queueRAM/ti_graph_link/schematics/ti_graph_link_serial_black/ti_graph_link_serial_black.kicad_sch

## KiCad design schematics/ti_graph_link_serial_black/ti_graph_link_serial_black.kicad_sch (2023-08-06)

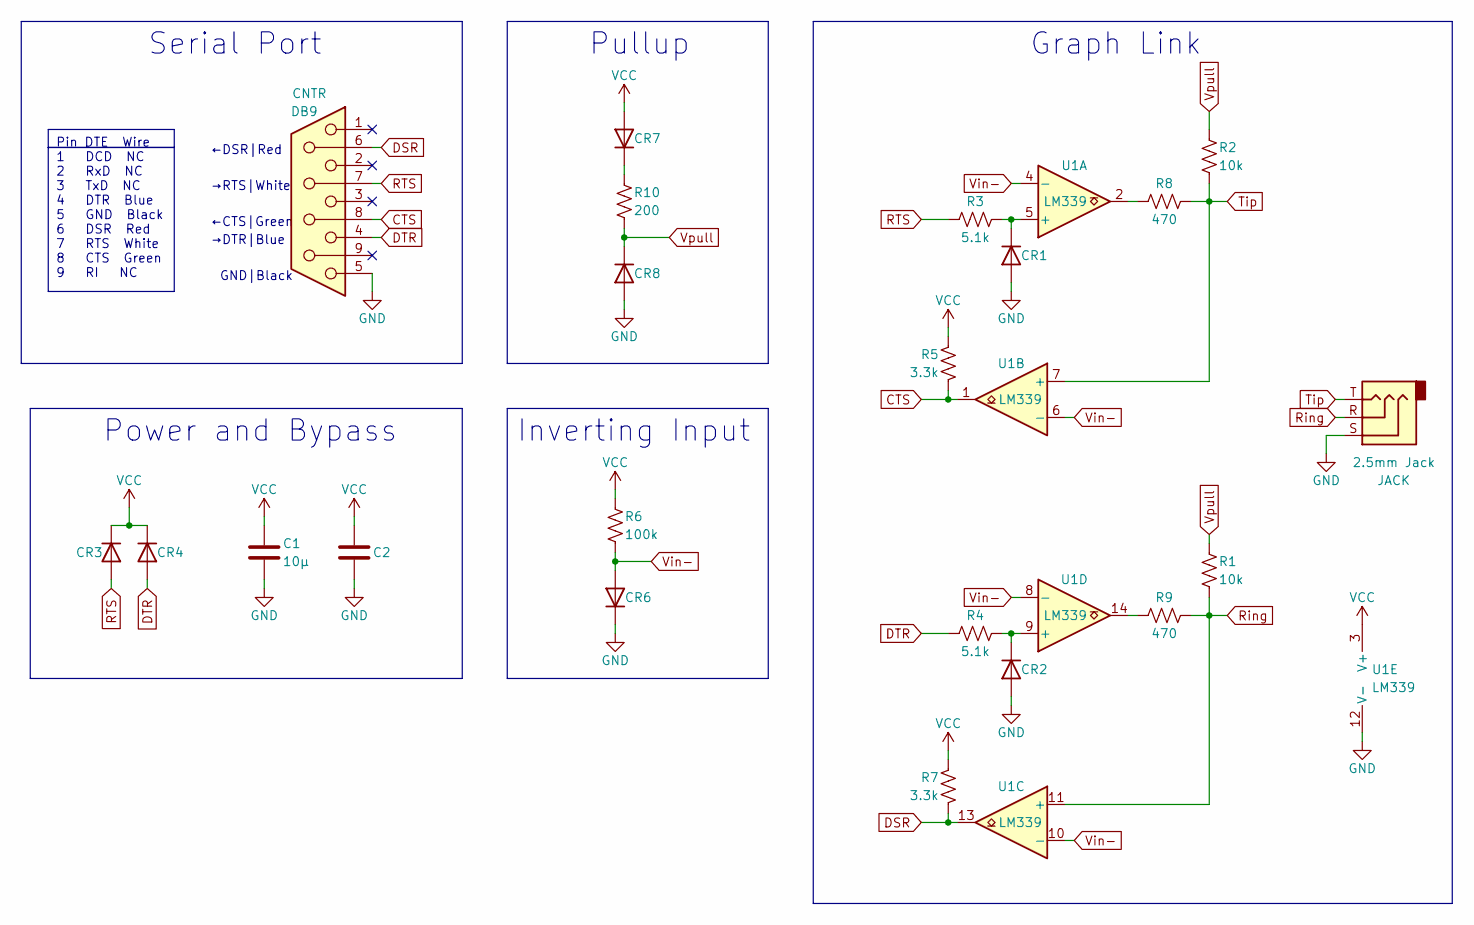
[picture p8: schematic ti_graph_link_serial_black.kicad_sch]

Parts:
C1: 10µ
C2: (no value)
CNTR: DB9
CR1, CR2, CR3, CR4, CR6, CR7, CR8: (no value)
JACK: 2.5mm Jack
R1, R2: 10k
R3, R4: 5.1k
R5, R7: 3.3k
R6: 100k
R8, R9: 470
R10: 200
U1: LM339

Connections:
CTS: CNTR.8, R5.2, U1.1
DSR: CNTR.6, R7.2, U1.13
DTR: CNTR.4, CR4.2 (A), R4.1
GND: C1.2, C2.2, CNTR.5, CR1.2 (A), CR2.2 (A), CR6.1 (K), CR8.2 (A), JACK.S, U1.12 (V-)
unnamed: CR1.1 (K), R3.2, U1.5 (+)
unnamed: CR2.1 (K), R4.2, U1.9 (+)
unnamed: CR7.1 (K), R10.1
unnamed: R8.1, U1.2
unnamed: R9.1, U1.14
RTS: CNTR.7, CR3.2 (A), R3.1
Ring: JACK.R, R1.2, R9.2, U1.11 (+)
Tip: JACK.T, R2.2, R8.2, U1.7 (+)
VCC: C1.1, C2.1, CR3.1 (K), CR4.1 (K), CR7.2 (A), R5.1, R6.1, R7.1, U1.3 (V+)
Vin-: CR6.2 (A), R6.2, U1.4 (-), U1.6 (-), U1.8 (-), U1.10 (-)
Vpull: CR8.1 (K), R1.1, R2.1, R10.2

Notes on the sheet:
Pin DTE Wire 1 DCD NC 2 RxD NC 3 TxD NC 4 DTR Blue 5 GND Black 6 DSR Red 7 RTS White 8 CTS Green 9 RI NC
→RTS|White
←CTS|Green
GND|Black
Serial Port
←DSR|Red
Graph Link
→DTR|Blue
Inverting Input
Pullup
Power and Bypass
