queueRAM/ti_graph_link/schematics/ti_graph_link_serial_gray/ti_graph_link_serial_gray.kicad_sch

## KiCad design schematics/ti_graph_link_serial_gray/ti_graph_link_serial_gray.kicad_sch (2025-07-07)

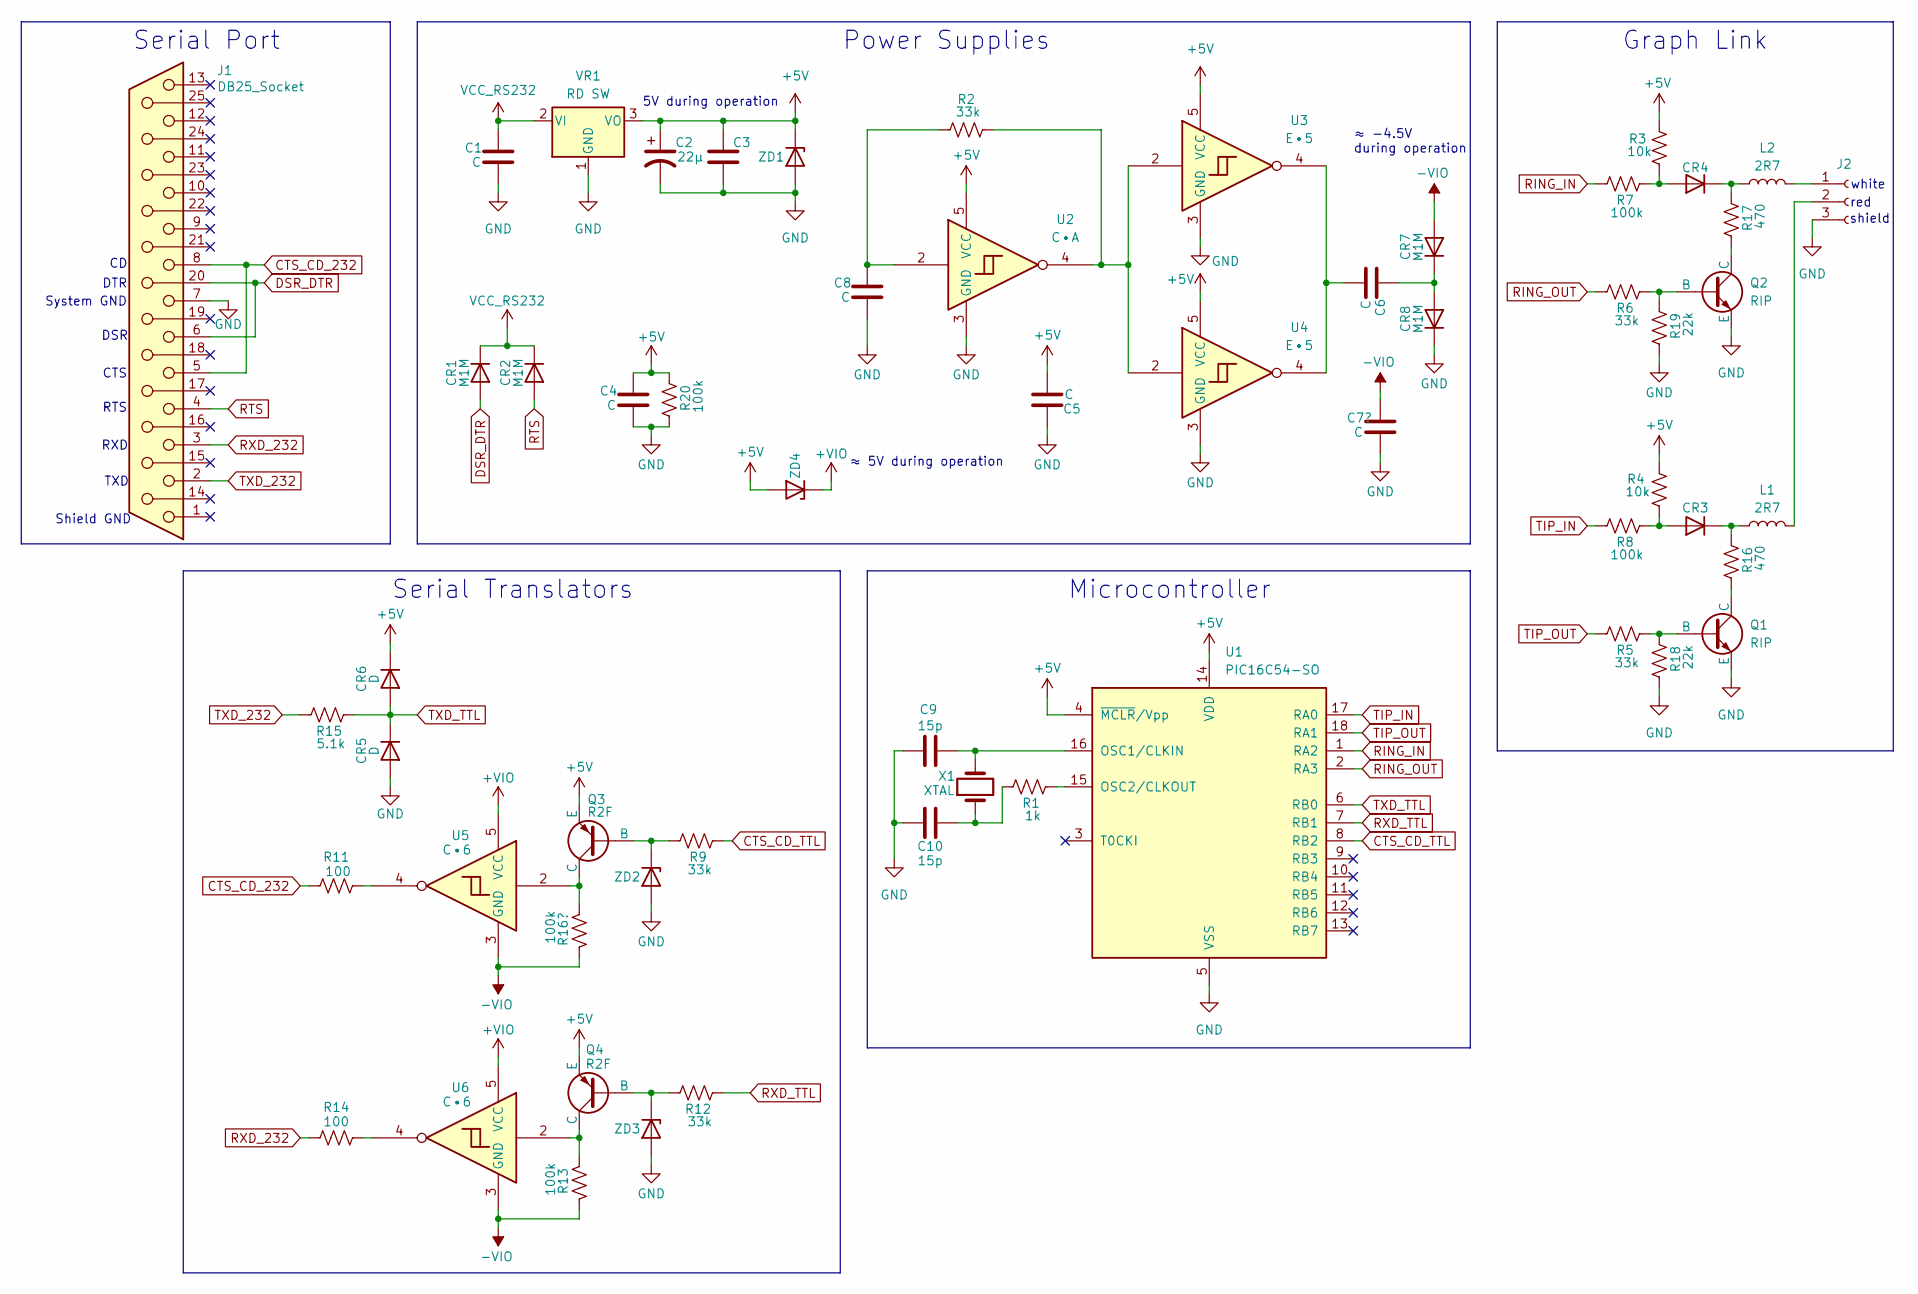
[picture p9: schematic ti_graph_link_serial_gray.kicad_sch]

Parts:
C1, C4, C5, C6, C8: C
C2: 22µ
C3: (no value)
C9, C10: 15p
CR1, CR2, CR7, CR8: M1M
CR3, CR4: (no value)
CR5, CR6: D
J1: DB25_Socket
J2: Conn_01x03_Socket
L1, L2: 2R7
Q1, Q2: RIP
Q3, Q4: R2F
R1: 1k
R2, R5, R6, R9, R12: 33k
R3, R4: 10k
R7, R8, R13, R20: 100k
R11, R14: 100
R15: 5.1k
R16, R17: 470
R18, R19: 22k
U1: PIC16C54-SO; SOIC-18W_7.5x11.6mm_P1.27mm
U2: C•A; SOT-23-5
U3, U4: E•5; SOT-23-5
U5, U6: C•6; SOT-23-5
VR1: RD SW; SOT-89-3
X1: XTAL
ZD1, ZD2, ZD3, ZD4: (no value)

Connections:
+5V: C2.1, C3.1, C4.1, C5.2, CR6.1 (K), Q3.3 (E), Q4.3 (E), R3.2, R4.2, R20.2, U1.4 (~MCLR/Vpp), U1.14 (VDD), U2.5 (VCC), U3.5 (VCC), U4.5 (VCC), VR1.3 (VO), ZD1.1 (K), ZD4.2 (A)
+VIO: U5.5 (VCC), U6.5 (VCC), ZD4.1 (K)
-VIO: CR7.2 (A), R13.1, U5.3 (GND), U6.3 (GND)
CTS_CD_232: J1.5, J1.8, R11.1
CTS_CD_TTL: R9.2, U1.8 (RB2)
DSR_DTR: CR1.2 (A), J1.6, J1.20
GND: C1.2, C2.2, C3.2, C4.2, C5.1, C8.2, C9.1, C10.1, CR5.2 (A), CR8.1 (K), J1.7, J2.3, Q1.3 (E), Q2.3 (E), R18.1, R19.1, R20.1, U1.5 (VSS), U2.3 (GND), U3.3 (GND), U4.3 (GND), VR1.1 (GND), ZD1.2 (A), ZD2.2 (A), ZD3.2 (A)
unnamed: C6.1, CR7.1 (K), CR8.2 (A)
unnamed: C6.2, U3.4, U4.4
unnamed: C8.1, R2.1, U2.2
unnamed: C9.2, U1.16 (OSC1/CLKIN), X1.2
unnamed: C10.2, R1.1, X1.1
unnamed: CR3.1 (K), L1.1, R16.2
unnamed: CR3.2 (A), R4.1, R8.2
unnamed: CR4.1 (K), L2.1, R17.2
unnamed: CR4.2 (A), R3.1, R7.2
unnamed: J2.1, L2.2
unnamed: J2.2, L1.2
unnamed: Q1.1 (C), R16.1
unnamed: Q1.2 (B), R5.2, R18.2
unnamed: Q2.1 (C), R17.1
unnamed: Q2.2 (B), R6.2, R19.2
unnamed: Q3.1 (C), U5.2
unnamed: Q3.2 (B), R9.1, ZD2.1 (K)
unnamed: Q4.1 (C), R13.2, U6.2
unnamed: Q4.2 (B), R12.1, ZD3.1 (K)
unnamed: R1.2, U1.15 (OSC2/CLKOUT)
unnamed: R2.2, U2.4, U3.2, U4.2
unnamed: R11.2, U5.4
unnamed: R14.2, U6.4
RING_IN: R7.1, U1.1 (RA2)
RING_OUT: R6.1, U1.2 (RA3)
RTS: CR2.2 (A), J1.4
RXD_232: J1.3, R14.1
RXD_TTL: R12.2, U1.7 (RB1)
TIP_IN: R8.1, U1.17 (RA0)
TIP_OUT: R5.1, U1.18 (RA1)
TXD_232: J1.2, R15.1
TXD_TTL: CR5.1 (K), CR6.2 (A), R15.2, U1.6 (RB0)
VCC_RS232: C1.1, CR1.1 (K), CR2.1 (K), VR1.2 (VI)

Notes on the sheet:
RXD
Shield GND
Serial Translators
Serial Port
Microcontroller
RTS
Graph Link
TXD
red
DSR
≈ -4.5V during operation
shield
≈ 5V during operation
DTR
white
5V during operation
System GND
CTS
Power Supplies
