queueRAM/ti_graph_link/schematics/ti_silver_link_a/ti_silver_link_a.kicad_sch

## KiCad design schematics/ti_silver_link_a/ti_silver_link_a.kicad_sch (2023-07-09)

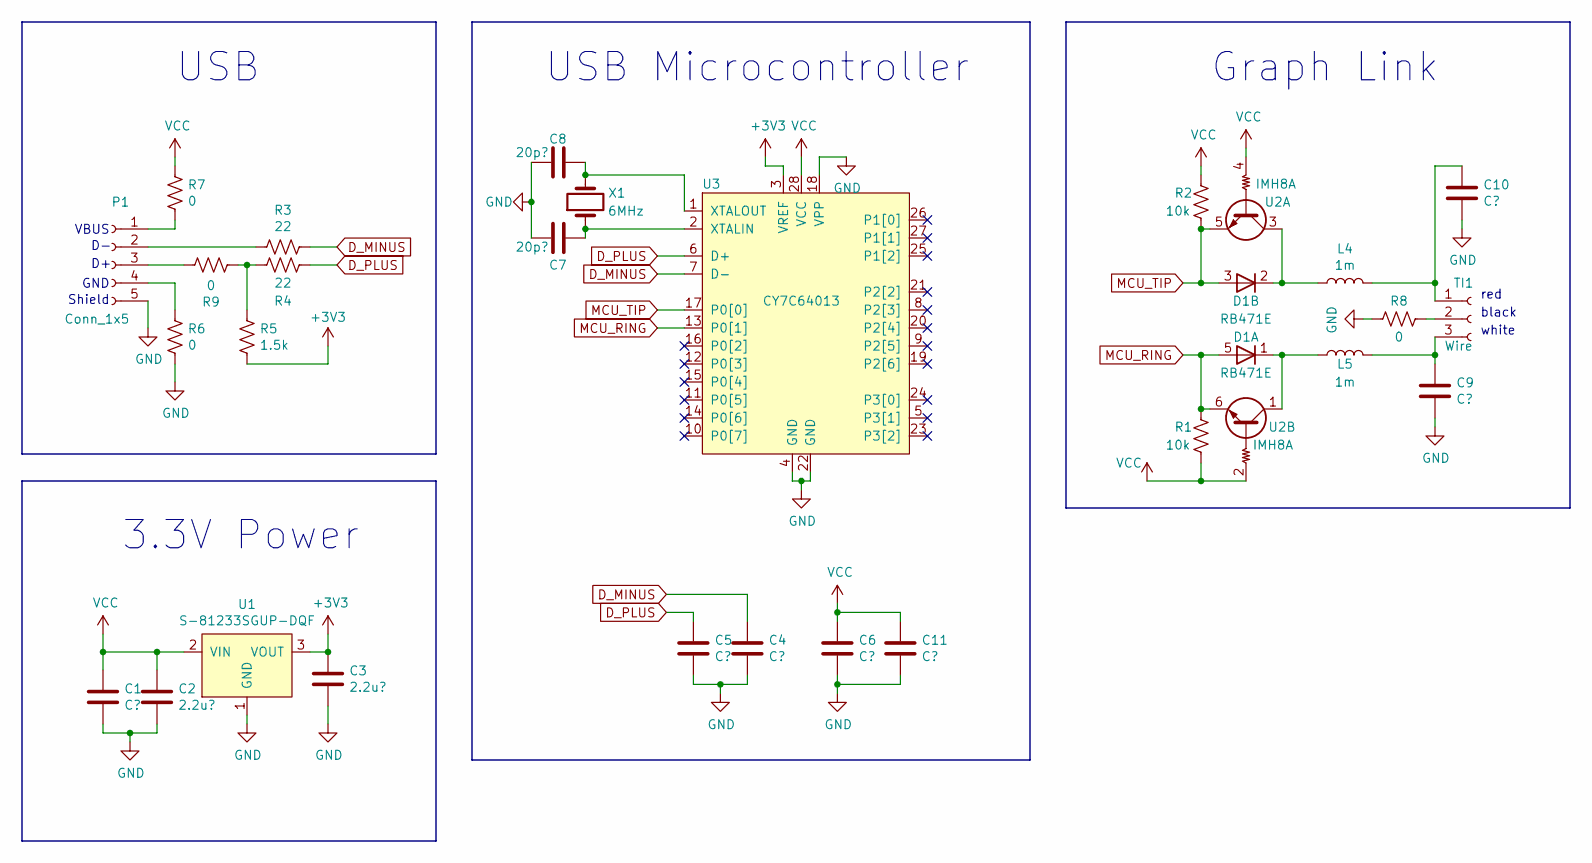
[picture p10: schematic ti_silver_link_a.kicad_sch]

Parts:
C1, C4, C5, C6, C9, C10, C11: C?
C2, C3: 2.2u?
C7, C8: 20p?
D1: RB471E
L4, L5: 1m
P1: Conn_1x5
R1, R2: 10k
R3, R4: 22
R5: 1.5k
R6, R7, R8, R9: 0
TI1: Wire
U1: S-81233SGUP-DQF
U2: IMH8A
U3: CY7C64013
X1: 6MHz

Connections:
+3V3: C3.1, R5.2, U1.3 (VOUT), U3.3 (VREF)
D_MINUS: C4.1, R3.1, U3.7 (D-)
D_PLUS: C5.1, R4.1, U3.6 (D+)
GND: C1.2, C2.2, C3.2, C4.2, C5.2, C6.2, C7.1, C8.1, C9.2, C10.2, C11.2, P1.5, R6.2, R8.2, U1.1 (GND), U3.4 (GND), U3.18 (VPP), U3.22 (GND)
MCU_RING: D1.5, R1.1, U2.6 (E1), U3.13 (P0[1])
MCU_TIP: D1.3, R2.2, U2.5 (E1), U3.17 (P0[0])
unnamed: C7.2, U3.2 (XTALIN), X1.1
unnamed: C8.2, U3.1 (XTALOUT), X1.2
unnamed: C9.1, L5.2, TI1.3
unnamed: C10.1, L4.2, TI1.1
unnamed: D1.1, L5.1, U2.1 (C1)
unnamed: D1.2, L4.1, U2.3 (C1)
unnamed: P1.1, R7.2
unnamed: P1.2, R3.2
unnamed: P1.3, R9.1
unnamed: P1.4, R6.1
unnamed: R4.2, R5.1, R9.2
unnamed: R8.1, TI1.2
VCC: C1.1, C2.1, C6.1, C11.1, R1.2, R2.1, R7.1, U1.2 (VIN), U2.2 (B1), U2.4 (B1), U3.28 (VCC)

Notes on the sheet:
black
Graph Link
3.3V Power
GND
USB Microcontroller
USB
red
Shield
white
VBUS
