queueRAM/ti_graph_link/schematics/ti_silver_link_b/ti_silver_link_b.kicad_sch

## KiCad design schematics/ti_silver_link_b/ti_silver_link_b.kicad_sch (2024-02-25)

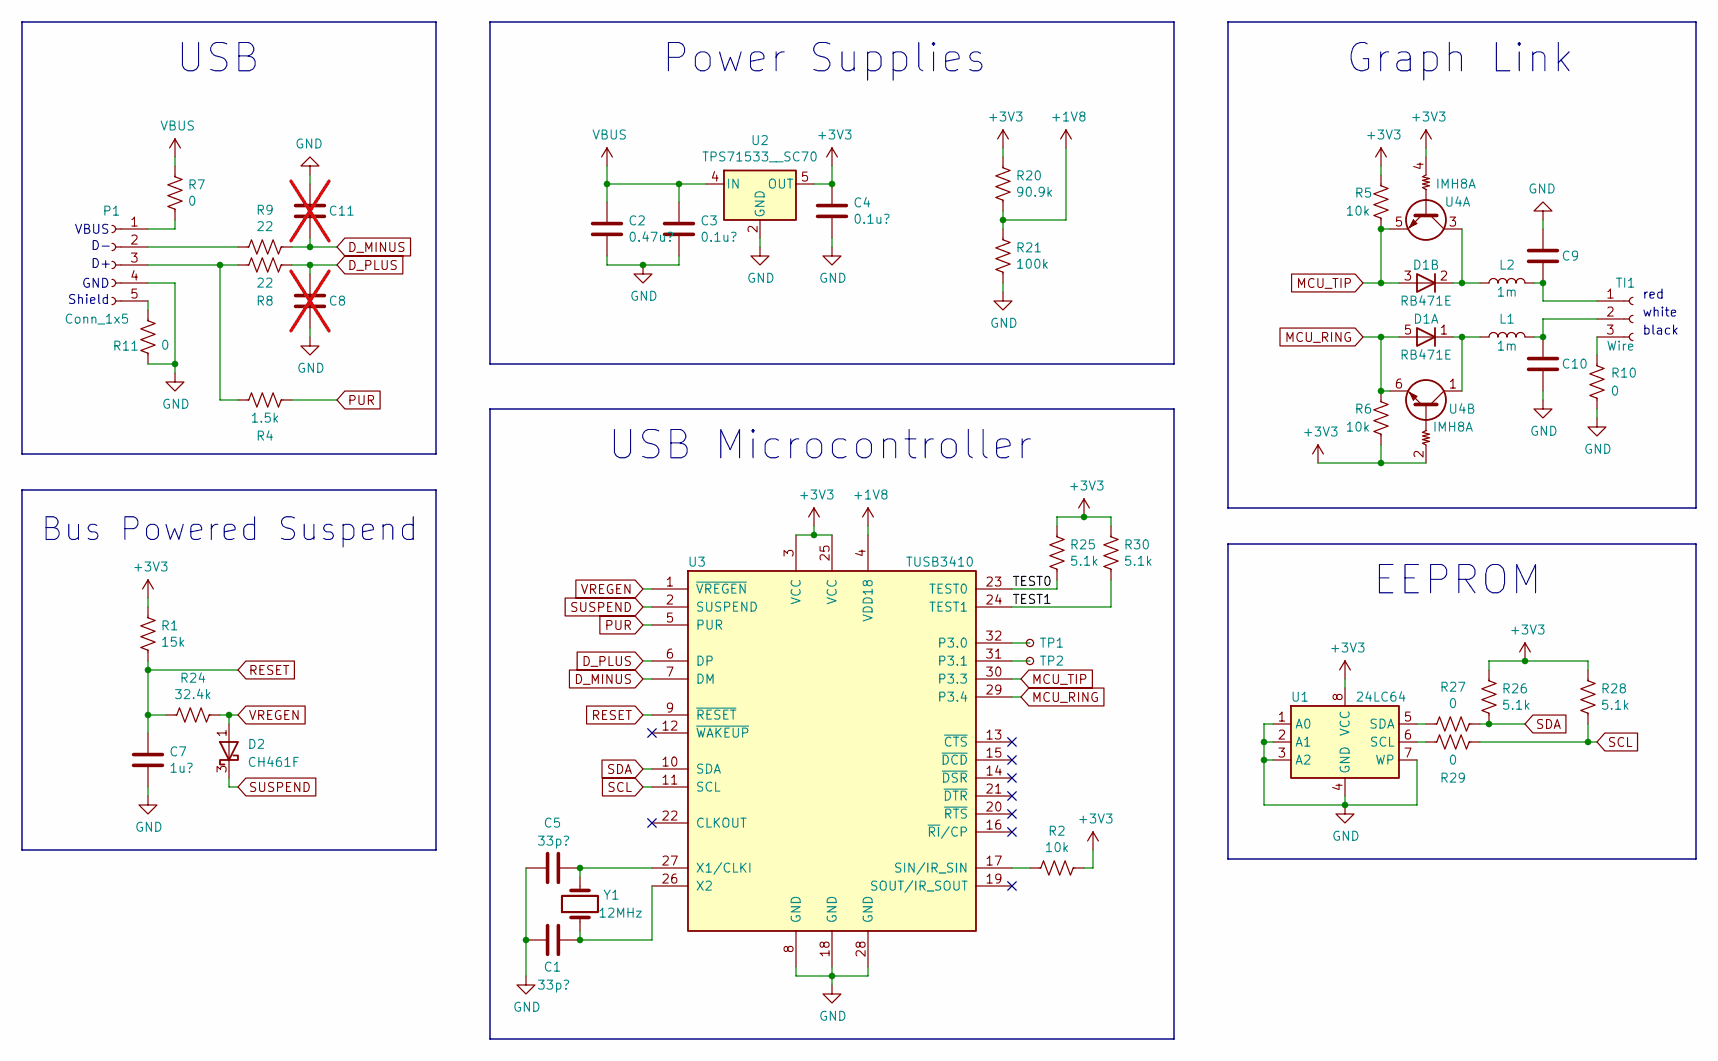
[picture p11: schematic ti_silver_link_b.kicad_sch]

Parts:
C1, C5: 33p?
C2: 0.47u?
C3, C4: 0.1u?
C7: 1u?
C8, C11: not fitted
C9, C10: (no value)
D1: RB471E
D2: CH461F; SOT-323_SC-70
L1, L2: 1m
P1: Conn_1x5
R1: 15k
R2, R5, R6: 10k
R4: 1.5k
R7, R10, R11, R27, R29: 0
R8, R9: 22
R20: 90.9k
R21: 100k
R24: 32.4k
R25, R26, R28, R30: 5.1k
TI1: Wire
TP1, TP2: (no value)
U1: 24LC64; SOIC-8_3.9x4.9mm_P1.27mm
U2: TPS71533__SC70; SOT-353_SC-70-5
U3: TUSB3410; VQFN-32-1EP_5x5mm_P0.5mm_EP3.5x3.5mm_ThermalVias
U4: IMH8A
Y1: 12MHz

Connections:
+1V8: R20.2, R21.1, U3.4 (VDD18)
+3V3: C4.1, R1.1, R2.1, R5.1, R6.2, R20.1, R25.1, R26.1, R28.1, R30.1, U1.8 (VCC), U2.5 (OUT), U3.3 (VCC), U3.25 (VCC), U4.2 (B1), U4.4 (B1)
D_MINUS: C11.2, R9.1, U3.7 (DM)
D_PLUS: C8.1, R8.1, U3.6 (DP)
GND: C1.1, C2.2, C3.2, C4.2, C5.1, C7.2, C8.2, C9.1, C10.2, C11.1, P1.4, R10.2, R11.2, R21.2, U1.1 (A0), U1.2 (A1), U1.3 (A2), U1.4 (GND), U1.7 (WP), U2.2 (GND), U3.8 (GND), U3.18 (GND), U3.28 (GND)
MCU_RING: D1.5, R6.1, U3.29 (P3.4), U4.6 (E1)
MCU_TIP: D1.3, R5.2, U3.30 (P3.3), U4.5 (E1)
unnamed: C1.2, U3.26 (X2), Y1.1
unnamed: C5.2, U3.27 (X1/CLKI), Y1.2
unnamed: C9.2, L2.2, TI1.1
unnamed: C10.1, L1.2, TI1.2
unnamed: D1.1, L1.1, U4.1 (C1)
unnamed: D1.2, L2.1, U4.3 (C1)
unnamed: P1.1, R7.2
unnamed: P1.2, R9.2
unnamed: P1.3, R4.2, R8.2
unnamed: P1.5, R11.1
unnamed: R2.2, U3.17 (SIN/IR_SIN)
unnamed: R10.1, TI1.3
unnamed: R27.2, U1.5 (SDA)
unnamed: R29.2, U1.6 (SCL)
unnamed: TP1.1, U3.32 (P3.0)
unnamed: TP2.1, U3.31 (P3.1)
PUR: R4.1, U3.5 (PUR)
RESET: C7.1, R1.2, R24.2, U3.9 (~RESET)
SCL: R28.2, R29.1, U3.11 (SCL)
SDA: R26.2, R27.1, U3.10 (SDA)
SUSPEND: D2.3 (K), U3.2 (SUSPEND)
TEST0: R25.2, U3.23 (TEST0)
TEST1: R30.2, U3.24 (TEST1)
VBUS: C2.1, C3.1, R7.1, U2.4 (IN)
VREGEN: D2.1 (A), R24.1, U3.1 (~VREGEN)

Notes on the sheet:
red
Bus Powered Suspend
GND
white
USB Microcontroller
Shield
VBUS
black
Graph Link
USB
EEPROM
Power Supplies
