queueRAM/ti_graph_link/schematics/ti_silver_link_breadboard/ti_silver_link_okrayo_breadboard.kicad_sch

## KiCad design schematics/ti_silver_link_breadboard/ti_silver_link_okrayo_breadboard.kicad_sch (2024-02-25)

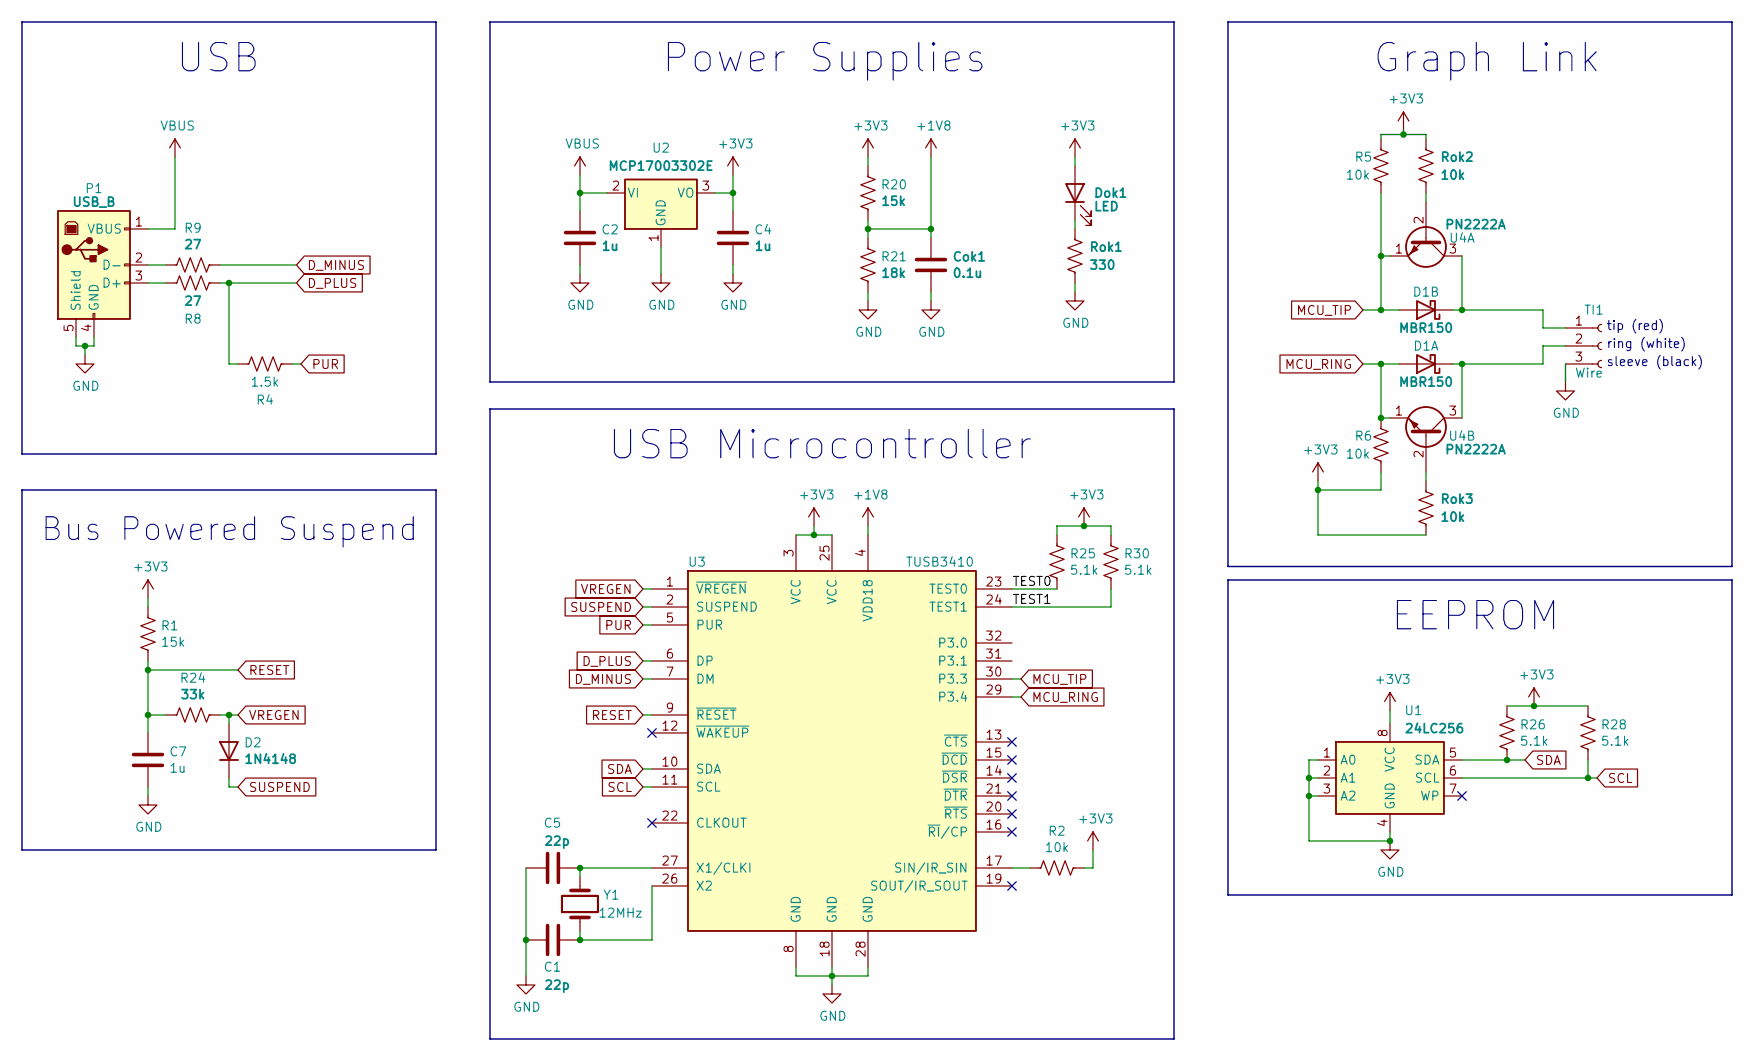
[picture p12: schematic ti_silver_link_okrayo_breadboard.kicad_sch]

Parts:
C1, C5: 22p
C2, C4, C7: 1u
Cok1: 0.1u
D1A, D1B: MBR150; D_DO-41_SOD81_P10.16mm_Horizontal
D2: 1N4148; SOT-323_SC-70
Dok1: LED
P1: USB_B
R1, R20: 15k
R2, R5, R6: 10k
R4: 1.5k
R8, R9: 27
R21: 18k
R24: 33k
R25, R26, R28, R30: 5.1k
Rok1: 330
Rok2, Rok3: 10k
TI1: Wire
U1: 24LC256
U2: MCP17003302E; TO-92_Inline
U3: TUSB3410; VQFN-32-1EP_5x5mm_P0.5mm_EP3.5x3.5mm_ThermalVias
U4A, U4B: PN2222A; TO-92_Inline
Y1: 12MHz

Connections:
+3V3: C4.1, Dok1.2 (A), R1.1, R20.1, R25.1, R26.1, R28.1, R30.1, U1.8 (VCC), U2.3 (VO)
D_MINUS: R9.1, U3.7 (DM)
D_PLUS: R4.2, R8.1, U3.6 (DP)
GND: C2.2, C4.2, Cok1.2, Rok1.2, TI1.3, U2.1 (GND)
MCU_RING: D1A.2 (A), R6.1, U3.29 (P3.4), U4B.1 (E)
MCU_TIP: D1B.2 (A), R5.2, U3.30 (P3.3), U4A.1 (E)
unnamed: C1.1, C5.1
unnamed: C1.2, U3.26 (X2), Y1.1
unnamed: C2.1, U2.2 (VI)
unnamed: C5.2, U3.27 (X1/CLKI), Y1.2
unnamed: Cok1.1, R20.2, R21.1
unnamed: D1A.1 (K), TI1.2, U4B.3 (C)
unnamed: D1B.1 (K), TI1.1, U4A.3 (C)
unnamed: Dok1.1 (K), Rok1.1
unnamed: P1.2 (D-), R9.2
unnamed: P1.3 (D+), R8.2
unnamed: P1.4 (GND), P1.5 (Shield)
unnamed: R2.2, U3.17 (SIN/IR_SIN)
unnamed: R5.1, Rok2.1
unnamed: R6.2, Rok3.2
unnamed: Rok2.2, U4A.2 (B)
unnamed: Rok3.1, U4B.2 (B)
unnamed: U1.1 (A0), U1.2 (A1), U1.3 (A2), U1.4 (GND)
unnamed: U3.8 (GND), U3.18 (GND), U3.28 (GND)
unnamed: U3.3 (VCC), U3.25 (VCC)
PUR: R4.1, U3.5 (PUR)
RESET: C7.1, R1.2, R24.2, U3.9 (~RESET)
SCL: R28.2, U1.6 (SCL), U3.11 (SCL)
SDA: R26.2, U1.5 (SDA), U3.10 (SDA)
SUSPEND: D2.3 (K), U3.2 (SUSPEND)
TEST0: R25.2, U3.23 (TEST0)
TEST1: R30.2, U3.24 (TEST1)
VREGEN: D2.1 (A), R24.1, U3.1 (~VREGEN)

Notes on the sheet:
ring (white)
sleeve (black)
USB
EEPROM
Graph Link
Power Supplies
Bus Powered Suspend
tip (red)
USB Microcontroller
